thewonderidiot/lachesis/docs/PS-2016042.pdf

J | ...

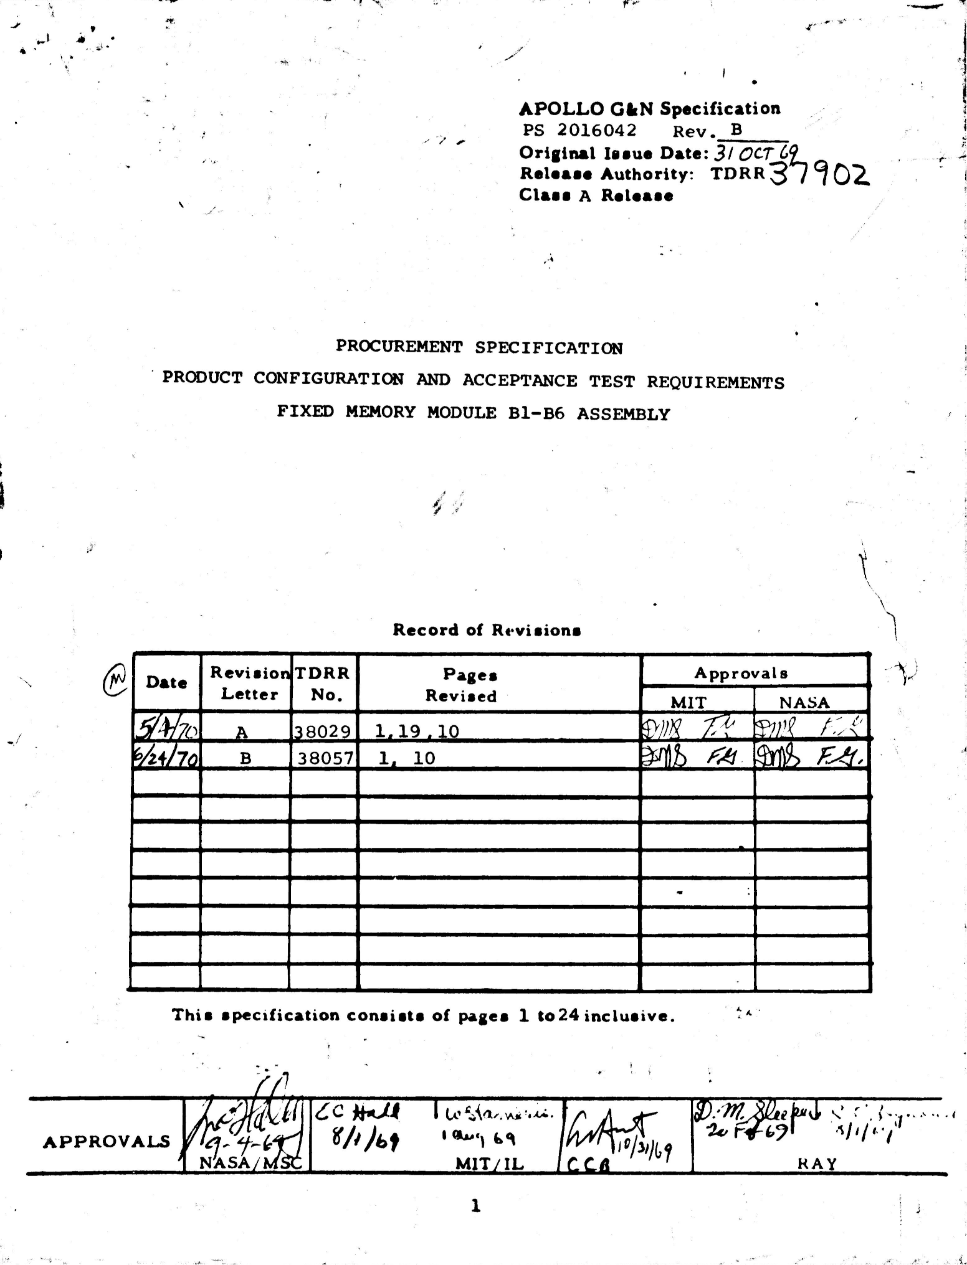
[picture p12: page 1]

/ -

APOLLO G•N Specification
PS 2016042 Rev._B __
Ori1tnal luue Date: 31 OC.i ti_ ReleaH Authority: TORR 3~7 '102. Claee A Relea••

PROCUREMENT SPECIFICATION
. PRODUCT CONFIGURATION AND ACCEPTANCE TEST REQUIREMENTS FIXED MEMORY MODULE Bl-B6 ASSEMBLY

i

\

Record of R .. vi ion■

Date Revi ior TORR | Paae• | Approvals
Letter | No. | Reviaed | MIT | NASA
'ilfli) | fr)Jl' t1" T'JJ'f 1 - ,, 10 | . | ~
A | 138029 1.19 | • / | '
~/2fl7ti | B | 38057 1. 10 | M') ~ | - ~ £,.!J,
. | :

Thi ■ apecificahon conei ta of paae• 1 &o24 inclu•ive.

u• i:Ja,._ ~ ,.~.
APPROVALS | I~•, bf\ | J0/31/~1
| MT IL

\
' I

~-

.j

I
'

APOLLO G&N Specification
PS 2016042

# Rev -----------

TABLE III

PIN NO. | . to | PIN NO. | PIN NO. | to | PIN NO •
402 | | 102 | 415 | | 115
405 | | 105 | 416 | | 116
406 | | 106 | 417 | | 117
407 | | 107 | 418 | | 118
408 | | 108 | 419 | | 119
409 | | 109 | 420 | | 120
410 | | 110 | 103 | | 104
411 | | 111 | . ·121 | | 122
412 | | 112 | 123 | | 124
413 . | | 113 | 404 | | 403
414 | | 114 | 422 | | 421
424 423
·-~
3 .1.5.3 The resistance~between pins 401 and 101 shall be not less than 6 ohms, nor more than 25 ohms.
3.1.6 | Input Voltage. | The assembly shall function as speci-
- fied herein when supplied with 14.0 ± 0.5 Vdc through a 3000 ohm± 5% re~istor· to pin 201.

*3.1.7 Program Content. When the contents of the Fixed Memory Module· are compared to the tes_ter tape programmed in accordance with ND 1002378, each core shall contain the correct information.

3.1.8 | Clear Mode. | With the input and timing waveforms as
specified ·in paragraph 4. 2 .8, the output waveform at the manufac-turer's test. sense line (pins 101 and 401) shall be as shown in Figure 3 and defined as.follows:
Zero . noise (v0 max)", measu~ed between 1.1 :t 0.05 Jl~ec

and 2.3 ± 0.05 µsec after the start of Logic Reset (FCR), shall be NMT 25 mv.
*NOTE: For tester tapes not prepared per ND 1002378 check sum . &- parity checks may be made in an AGC computer·.

r

,·

7

- '.

.,
,,
APOLLO G&N Specification
PS 2016042 '!
Rev - A
. .,

' 3.1.12 Vacuum. Th• IIOdule hall be capable of operating a ■ part of an AGC in an atmo phere of NMT 1 mm/Hg with coldplate coolant temperature at 35 .! 5°F. It hall produce the proper Self-Check and Parity Check■•• applicable to that particular
-· | progra■ | sembly of which the module ■ a part. ,
3.2 | .. PRODUCT CONFIGURATION | ' .-• ·- - - .
3.2.1 | Drawings. 'the configuration of the assembly shall be
in accordance with APOLLO G&N Dwgs. 2003972/2010802 and a}.l .. ,
·- drawing ■ and engineering data referenced thereon. | ~- _
3.2.2 | Weight. Weight of' the lllOdule hall be recorded.
4. QUALITY ASSUJUUfCB PROVISIONS .

4.1 GENERAL. The reapon ible contractor of the as embly , ahall be reaponaible for the accomplishment of each test required her•in. See Table IV. Product Perfonnance and Configuration kequirement/Quality Verification Croaa Reference Index.

;
" ·•;

;e;,•''O?.':t
,;~~ . i

Requirement ■
3~1.1
3.1.2
3.1.3
3.1.4
3.1.5.l
3.1.5.2
3.1.5.3
3.1. 7
3.1.8
3.1.9.l
3.1.9.2
3.1.9.3
·3.1.9.4
3.1.10.l
3.1.10.2
3.1.10.3
3 .1.11
3. l.12
3. 2 .·l'
3.2.2 ·,t

TABLE IV

.• .. ,.,-·,.
Verification
4.2.2
4.2.3 :;·
4.2.4
4.2.5
4.2.6.l
4.2.6.2
4.2.6.3
4.2.7
4.2.8
4.2.9.l
4.2.9.2
4.2.9.3
4.2.9.4
4.3.1.1
4.3.l.2
4.3.l.3
4.3.2
4.3.3
4.2.1
4.2.10

'. '

"

A2J2licable

"'

04255
04255
04255
04255
04255
04255
04255
04255
04255
04255 .
042C,5
04255
04255
04255
04255
04256 ., 04255

JDC

•

04257 or 04258
- ! | 04255
'' | 04255

'.
' ' . '°'!fl~-~ ·• • (" .. , .,.,

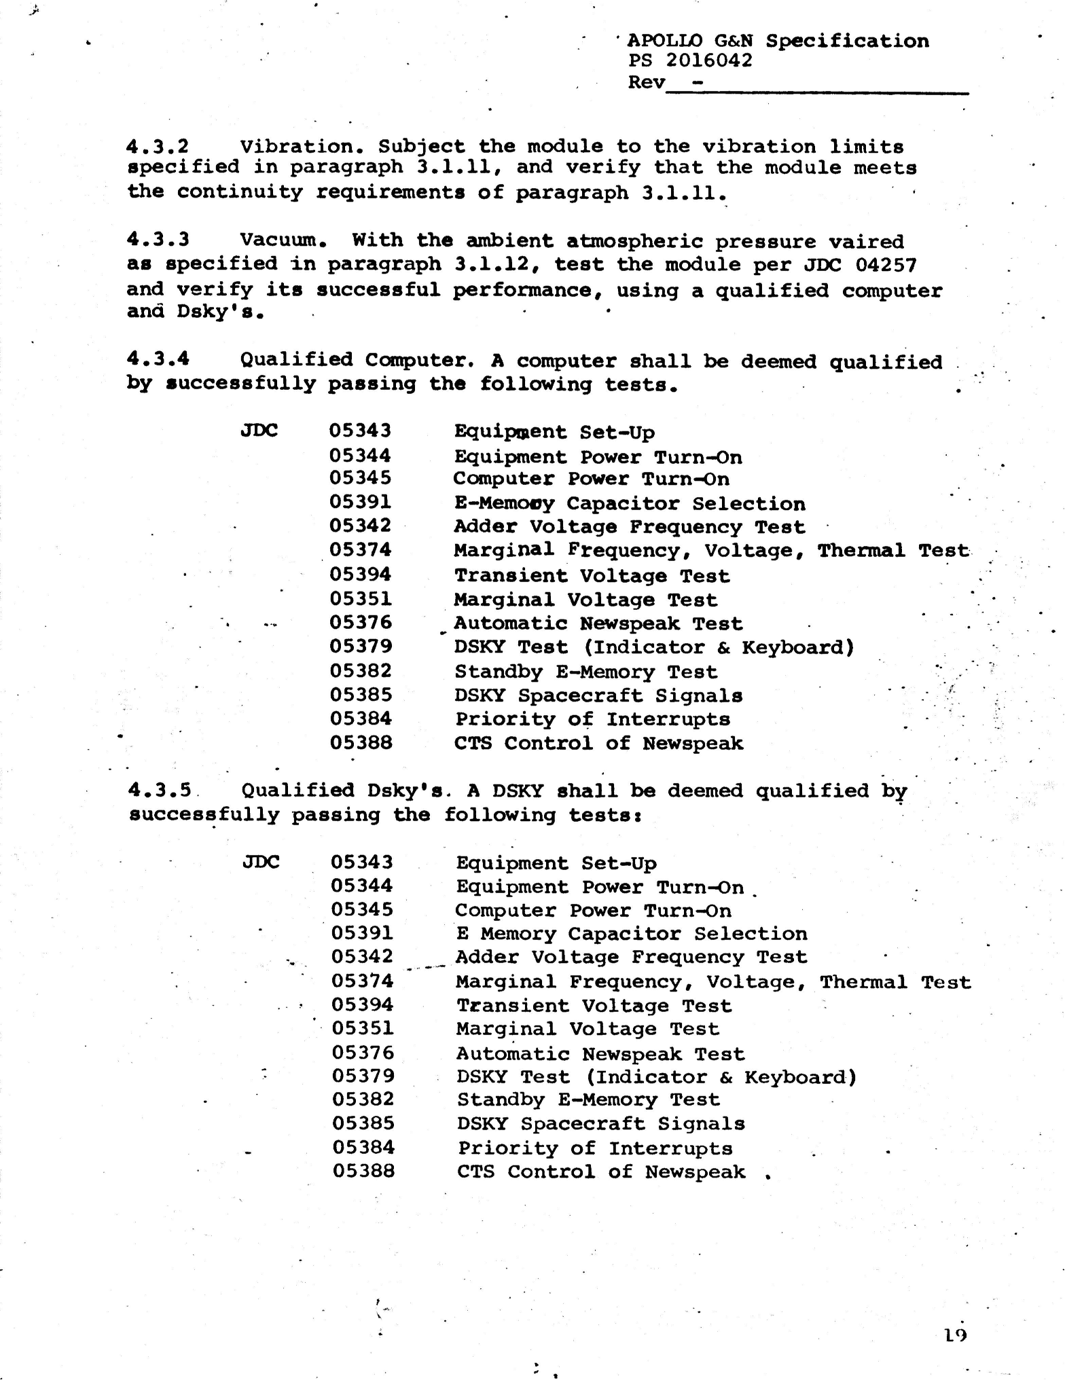
[picture p13: page 4]

;.
- APOLLO G&N Specification PS 2016042
Rev -

4.3.2 Vibration. Subject the module to the vibration limits specified in paragraph 3 . 1.11, and verify that the module meets the continuity requirements of paragraph 3 .1.11._

4.3.3 Vacuum. With the ambient atmospheric pressure vaired as specified in paragraph 3.1.12, test the module per JDC 04257 and verify its successful performance, using a qualified computer and Dsky's.

### 4.3.4 Qualified Computer. A computer shall be deemed qualified

by auccessfully passing the following tests.

JDC | EquiPQlent Set-Up
Equipment Power Turn-On
Computer Power Turn~n
E-Memoc,y Capacitor Selection Adder Voltage Frequency Test

05343
05344
05345
05391
05342
05374
05394
05351
05376
05379
05382
05385
05384
05388

Marginal Frequency, Voltage, Thermal Test Transient Voltage Test
Marginal Voltage Test
.Automatic Newspeak Test
DSKY Test (Indicator & Keyboard) Standby E-Memory Test
DSKY Spacecraft Signals
Priority o~ Interrupts
CTS Control of Newspeak

### 4.3.5 Qualified Dsky's. A DSKY shall be deemed qualified b¥

succes~fully passing the following testes

JDC

Equipment Set-Up
Equipment Power Turn-On .
Computer Power Turn-On
E Memory Capacitor Selection _ Adder Voltage Frequency Test

05343
05344
05345
05391
05342
05374
05394
05351
05376
05379
05382
05385
05384
05388

Marginal Frequency, Voltage, Thermal Test

,

\

Tcansient Voltage Test
Marg~nal Voltage Test
Automatic Newspeak Test
DSKY Test (Indicator & Keyboard) Standby E-Memory Test
DSKY Spacecraft Signals
Priority of Interrupts
CTS Control of Newspeak
