thewonderidiot/lachesis/gui/lachesis.py

#!/usr/bin/env python3
import sys
from PySide2.QtWidgets import QApplication
from main_window import MainWindow

if __name__ == '__main__':
    app = QApplication(sys.argv)
    window = MainWindow(None, app)
    window.show()
    app.exec_()
